sy2002/TeleBall/doc/cad/16teleballs.jpg

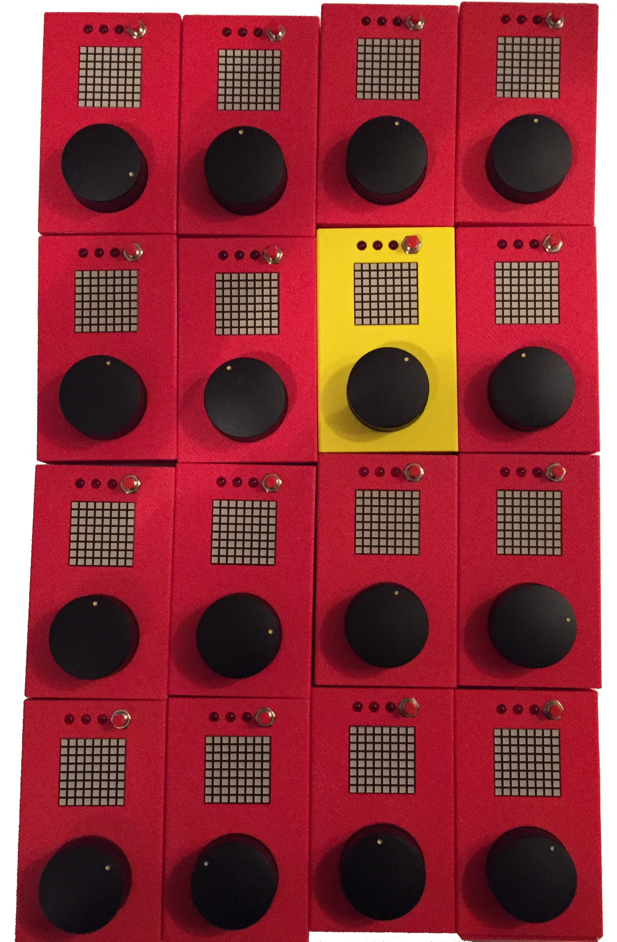
doc/cad/16teleballs.jpg
