sy2002/TeleBall/doc/cad/case1.png

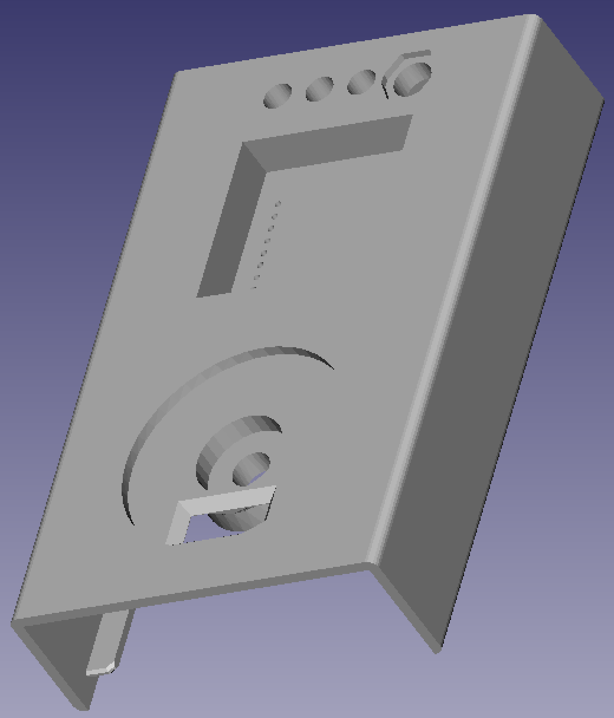
doc/cad/case1.png
