sy2002/TeleBall/doc/cad/case2.png

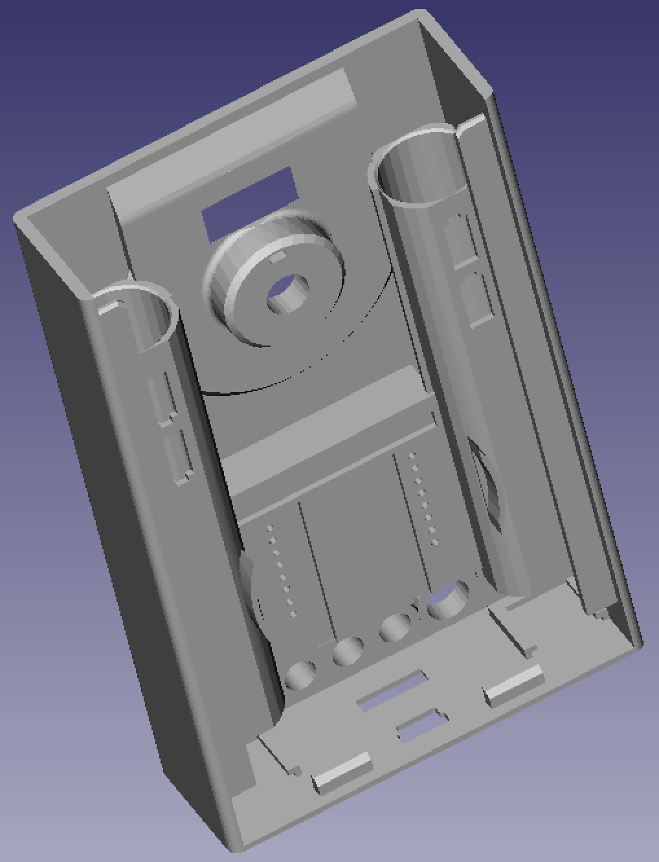
doc/cad/case2.png
