sy2002/TeleBall/doc/cad/lid1.png

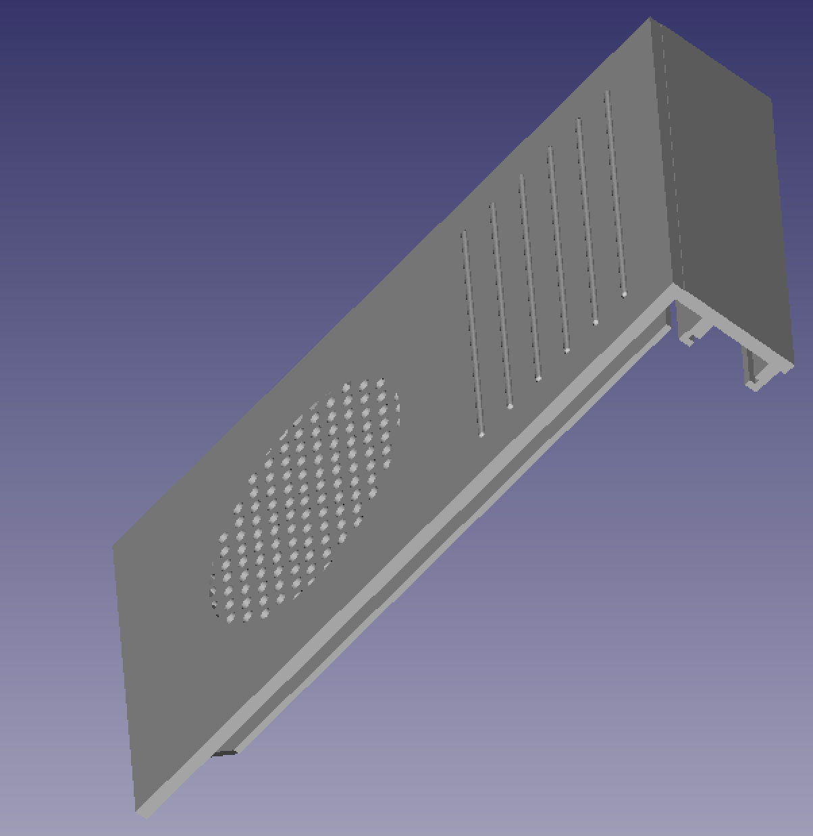
doc/cad/lid1.png
