sy2002/TeleBall/doc/cad/lid2.png

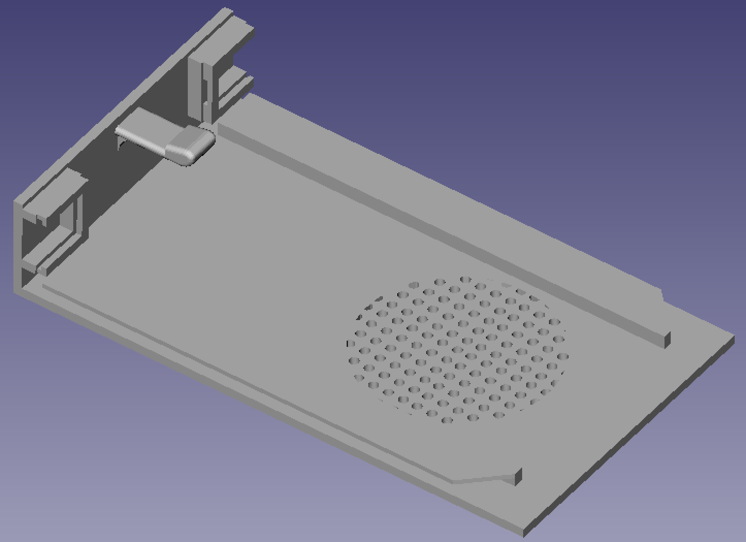
doc/cad/lid2.png
