sy2002/TeleBall/doc/cad/photo1.jpg

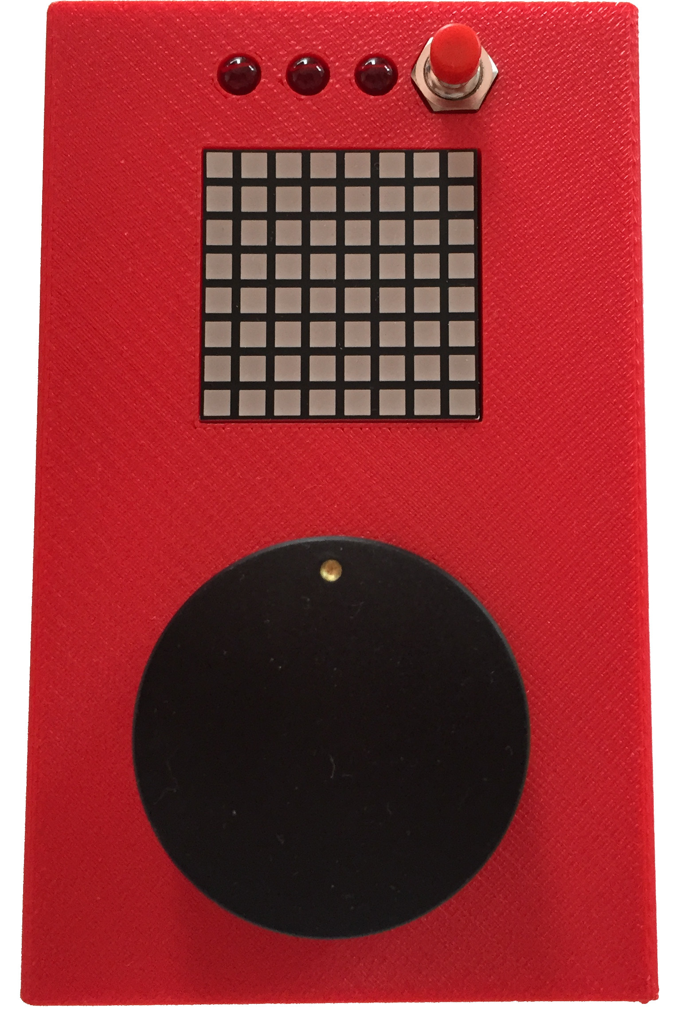
doc/cad/photo1.jpg
