sy2002/TeleBall/doc/cad/photo2.jpg

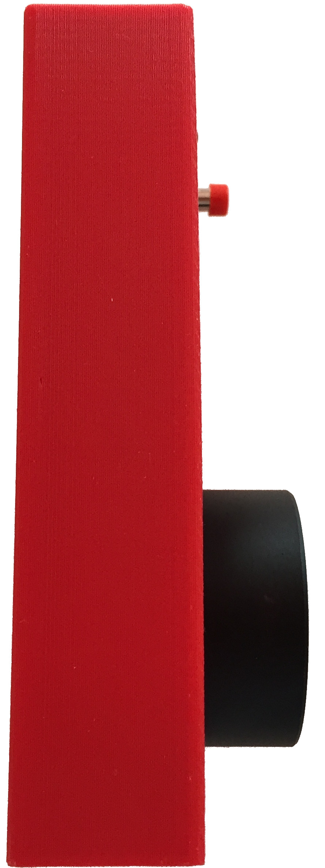
doc/cad/photo2.jpg
