sy2002/TeleBall/doc/cad/photo3.jpg

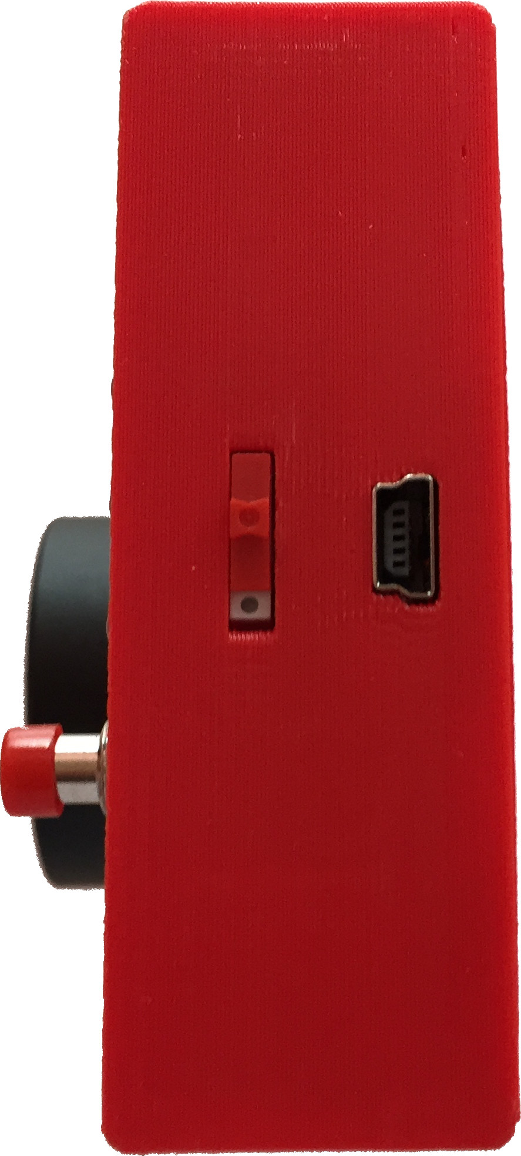
doc/cad/photo3.jpg
