sy2002/TeleBall/doc/cad/photo4.jpg

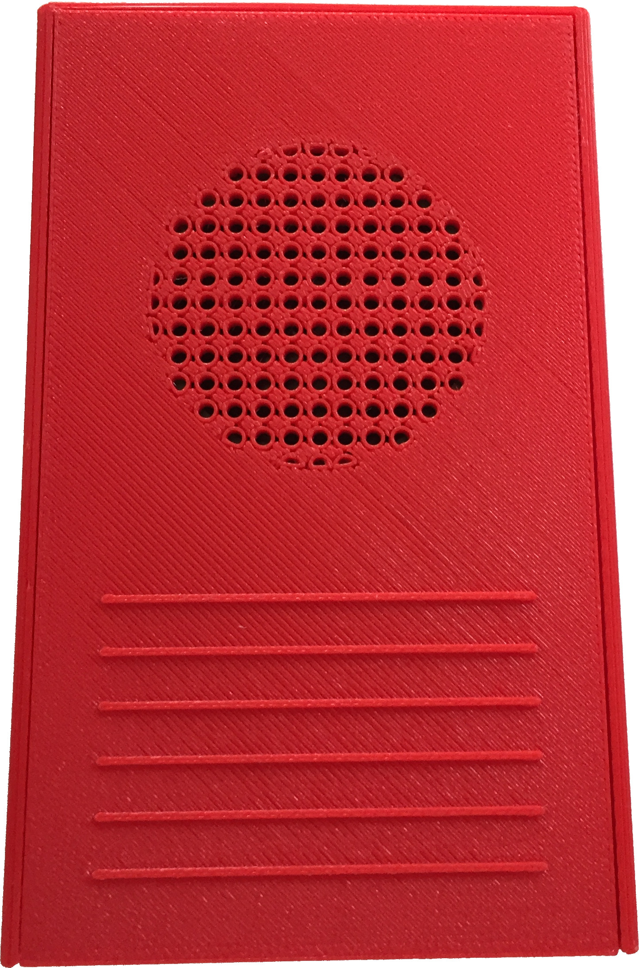
doc/cad/photo4.jpg
