sy2002/TeleBall/doc/cad/photo5.jpg

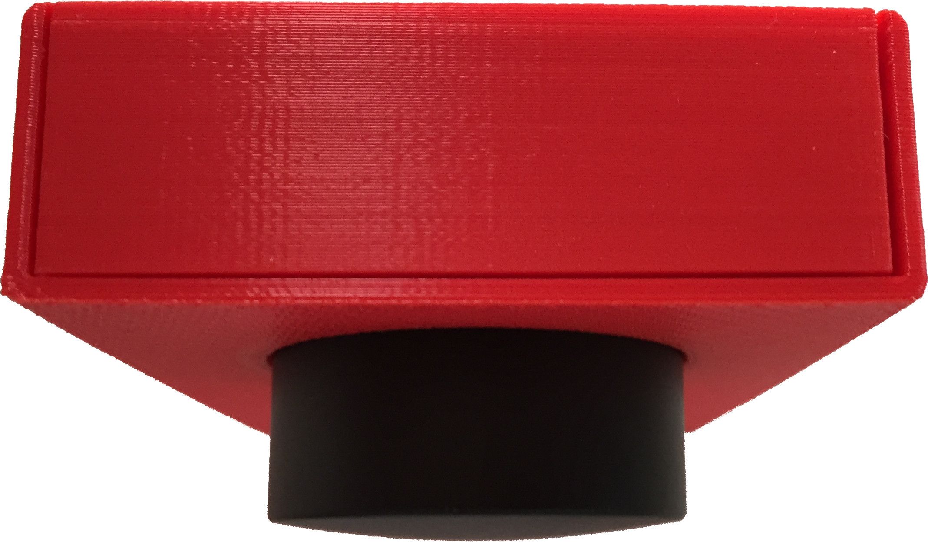
doc/cad/photo5.jpg
