sy2002/TeleBall/doc/cad/photo6.jpg

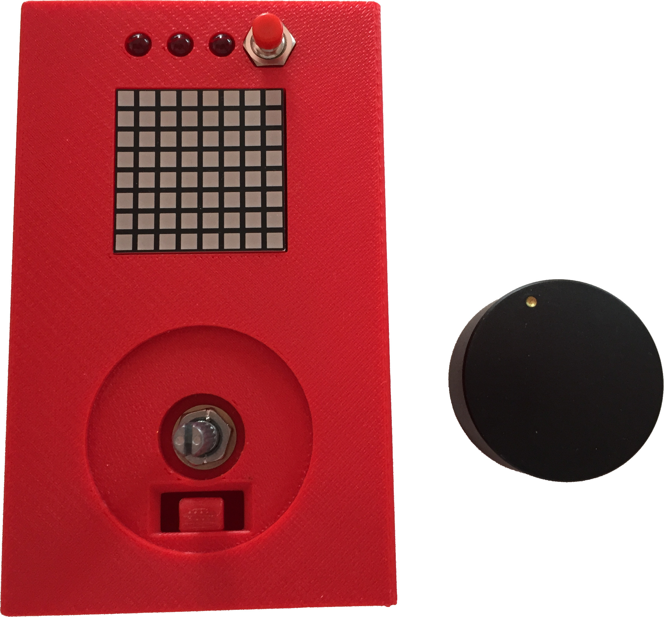
doc/cad/photo6.jpg
