sy2002/TeleBall/doc/cad/photo7.jpg

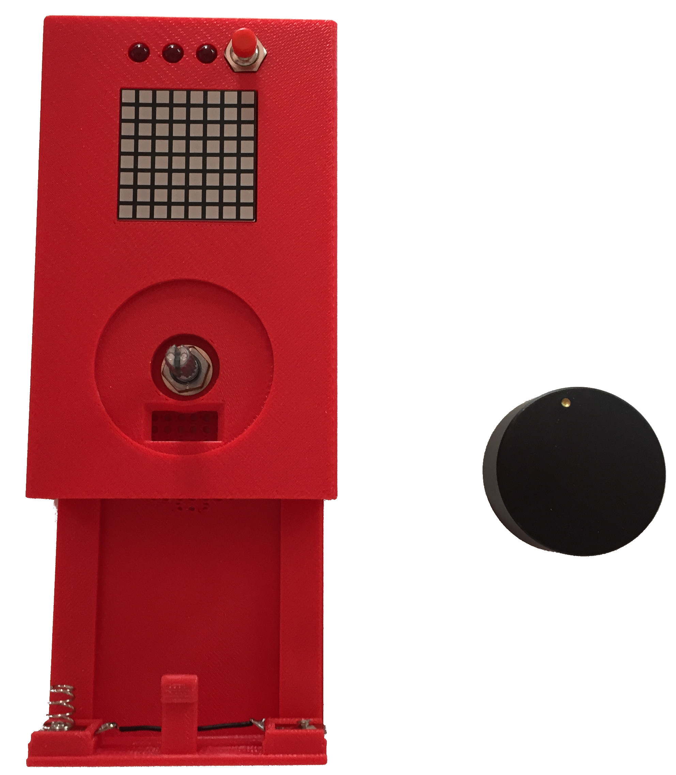
doc/cad/photo7.jpg
