sy2002/TeleBall/doc/cad/photo8.jpg

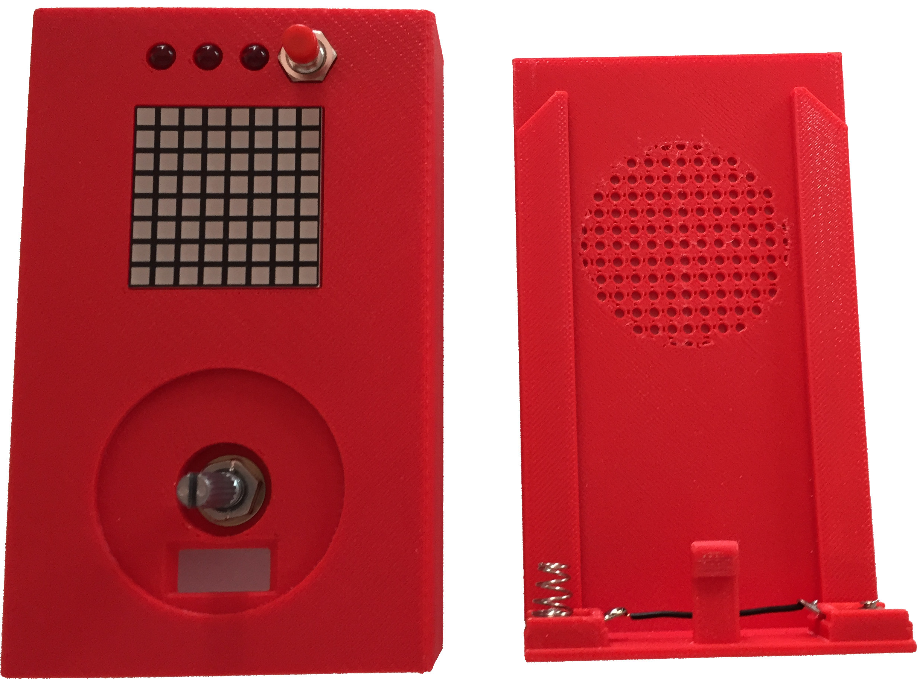
doc/cad/photo8.jpg
