sy2002/TeleBall/doc/cad/photo9.jpg

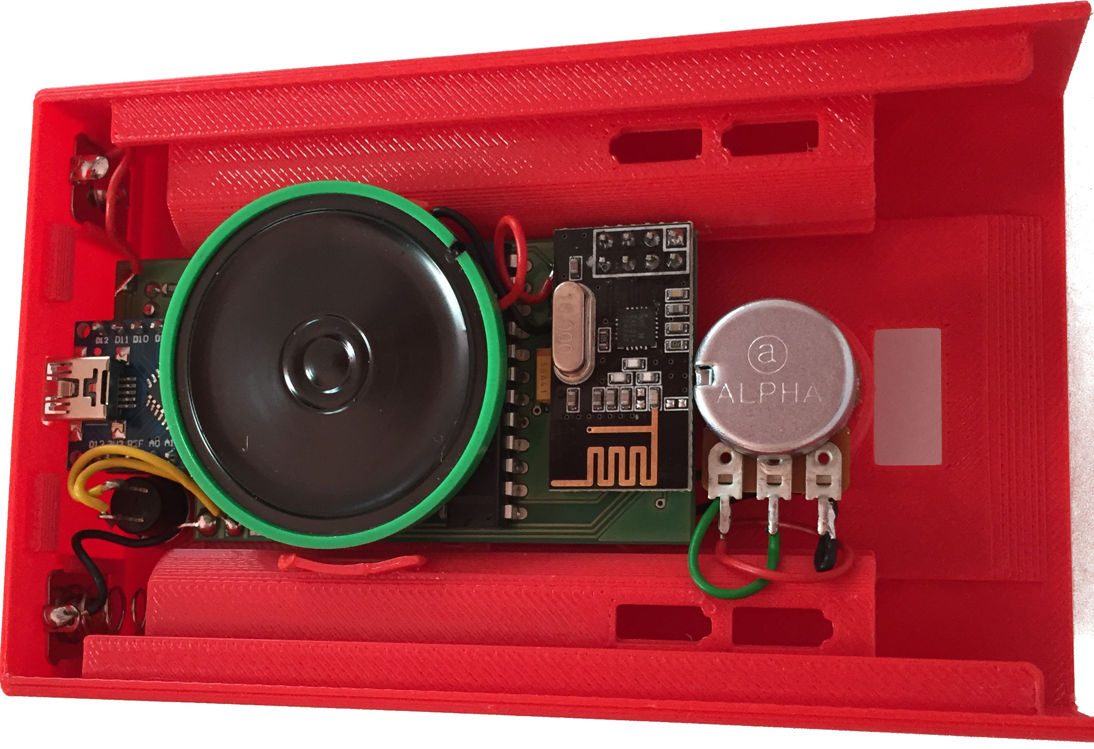
doc/cad/photo9.jpg
