sy2002/TeleBall/doc/cad/photo10.jpg

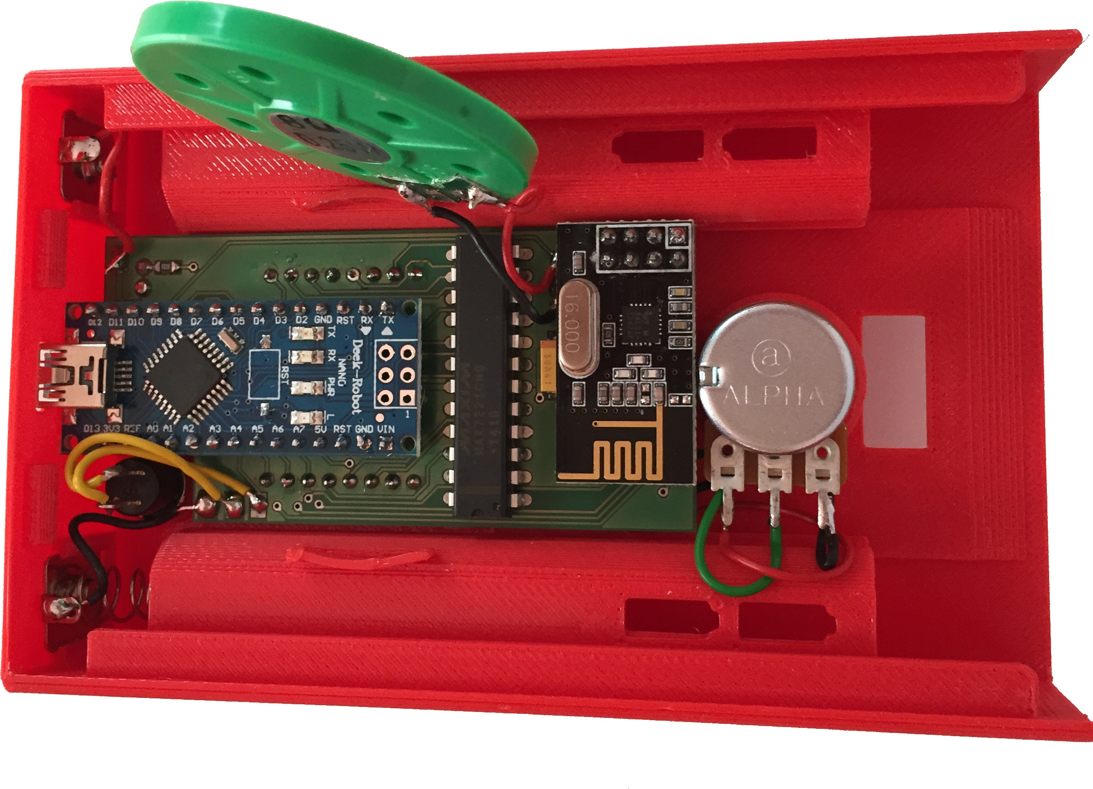
doc/cad/photo10.jpg
