sy2002/TeleBall/doc/cad/photo_case1.jpg

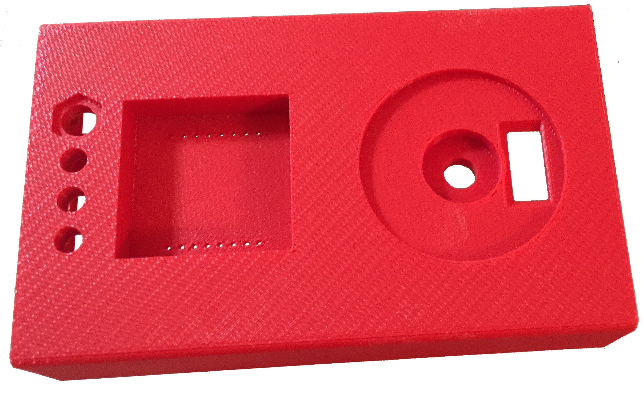
doc/cad/photo_case1.jpg
