sy2002/TeleBall/doc/cad/photo_case2.jpg

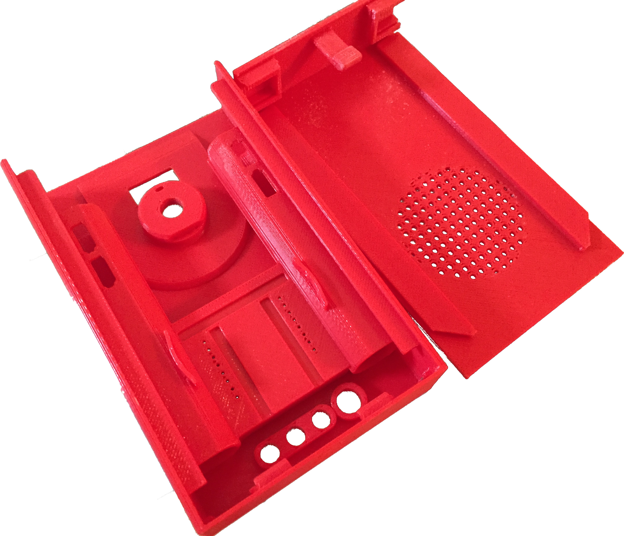
doc/cad/photo_case2.jpg
