sy2002/TeleBall/doc/cad/thumb5.jpg

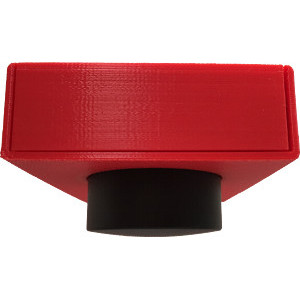
doc/cad/thumb5.jpg
