sy2002/TeleBall/doc/images/play_breakout.jpg

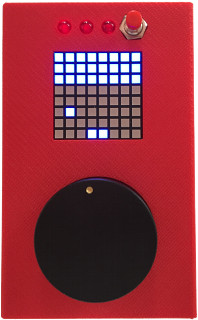
doc/images/play_breakout.jpg
