sy2002/TeleBall/doc/images/play_overview.jpg

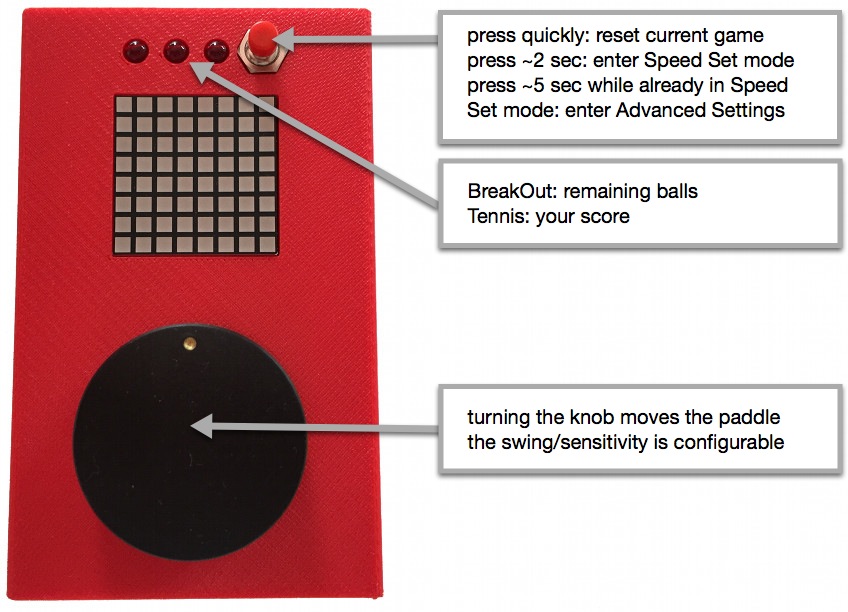
doc/images/play_overview.jpg
