sy2002/TeleBall/doc/images/play_tennis.jpg

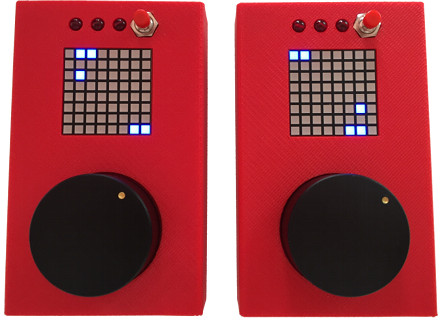
doc/images/play_tennis.jpg
